echolevel/open-amiga-sampler/smd-fork/open-amiga-sampler-smd.jpg

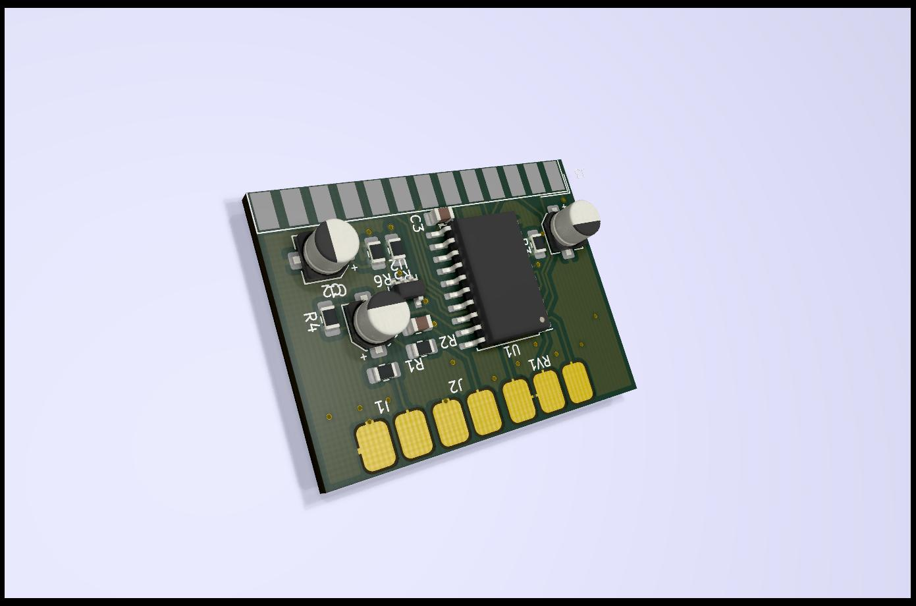
smd-fork/open-amiga-sampler-smd.jpg
