echolevel/open-amiga-sampler/smd-fork/open-sampler-smd-d-shell.png

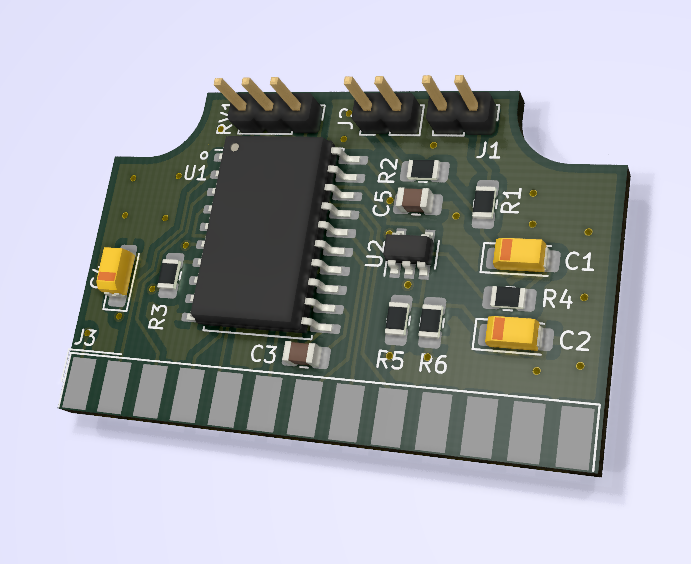
smd-fork/open-sampler-smd-d-shell.png
