echolevel/open-amiga-sampler/img/tester.jpg

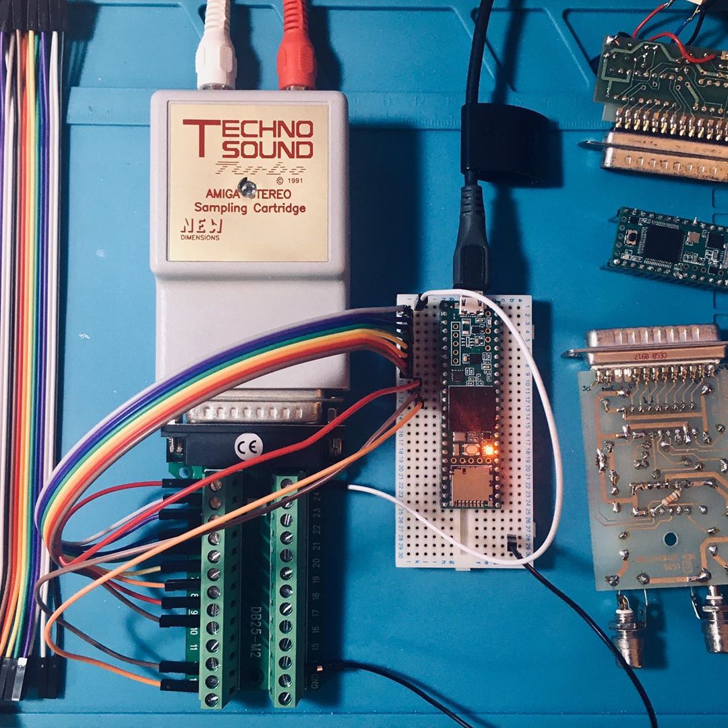
img/tester.jpg
